SharkPenPen/gamebub-handheld/python/gameboy_ps/__main__.py

#!/usr/bin/env python3

"""
Zynq PS side of the Gameboy, using the Pynq API to provide input and ROM loading.

Must be run as root.
"""

import logging
logging.basicConfig(format='[%(asctime)s][%(levelname)s] %(message)s', level=logging.DEBUG)
import sys
from pathlib import Path

from . import system

rom_directory = Path(sys.argv[1])
system = system.System(rom_directory)
system.start()
