SharkPenPen/gamebub-handheld/firmware/handheld/build.rs

fn main() {
    embuild::espidf::sysenv::output();

    slint_build::compile_with_config(
        "res/ui/main.slint",
        slint_build::CompilerConfiguration::new()
            .embed_resources(slint_build::EmbedResourcesKind::EmbedForSoftwareRenderer),
    )
    .unwrap();
}
