SharkPenPen/gamebub-handheld/fpga/sim/audio.hpp

#pragma once

#include <filesystem>
#include <fstream>

#include <SDL2/SDL.h>

const int AUDIO_CHANNELS = 2;

class Audio {
public:
    Audio(std::filesystem::path save_path);
    ~Audio();

    // Push samples (up to the maximum limit).
    // Each sample is signed (left, right) pair.
    void push(int16_t* data, uint32_t length);

private:
	SDL_AudioDeviceID device;
	std::ofstream output;
};
